tulip/gizmo/MicroWordClock2-Arduino/english.h

/*

 A*TWENTY
 FIVEHALF
 QUARTER*
 PAST*TO*
 FIVEIGHT
 SIXTHREE
 TWELEVEN
 FOURNINE
 
 // */

const int min_offset=7; // 12:00 + 5*7 min = twentyfive to ONE

const char minutes[12][8] ={
  { // o'clock
    0B00000000,
    0B00000000,
    0B00000000,
    0B00000000,
    0B00000000,
    0B00000000,
    0B00000000,
    0B00000000
  }
  , { // five past
    0B00000000,
    0B11110000,
    0B00000000,
    0B11110000,
    0B00000000,
    0B00000000,
    0B00000000,
    0B00000000
  }
  , { // ten past
    0B00101100,
    0B00000000,
    0B00000000,
    0B11110000,
    0B00000000,
    0B00000000,
    0B00000000,
    0B00000000
  }
  ,{ // quarter past
    0B00000000,
    0B00000000,
    0B11111110,
    0B11110000,
    0B00000000,
    0B00000000,
    0B00000000,
    0B00000000
  }
  ,{ // twenty past
    0B00111111,
    0B00000000,
    0B00000000,
    0B11110000,
    0B00000000,
    0B00000000,
    0B00000000,
    0B00000000
  }
  ,{ // twentyfive past
    0B00111111,
    0B11110000,
    0B00000000,
    0B11110000,
    0B00000000,
    0B00000000,
    0B00000000,
    0B00000000
  }
  ,{ // half past
    0B00000000,
    0B00001111,
    0B00000000,
    0B11110000,
    0B00000000,
    0B00000000,
    0B00000000,
    0B00000000
  }
  ,{ // twentyfive to
    0B00111111,
    0B11110000,
    0B00000000,
    0B00000110,
    0B00000000,
    0B00000000,
    0B00000000,
    0B00000000
  }
  ,{ // twenty to
    0B00111111,
    0B00000000,
    0B00000000,
    0B00000110,
    0B00000000,
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
  }
  ,{ // eleven
    0B00000000,
    0B00000000,
    0B00000000,
    0B00000000,
    0B00000000,
    0B00000000,
    0B00111111,
    0B00000000
  }
};

const char blinky[8] ={
  0B01000000,
  0B00000000,
  0B00000000,
  0B00000000,
  0B00000000,
  0B00000000,
  0B00000000,
  0B00000000
};
